SPAC3TRUK/Air-Link-Esp8266-/Progettazione_e_Documentazione/1.png

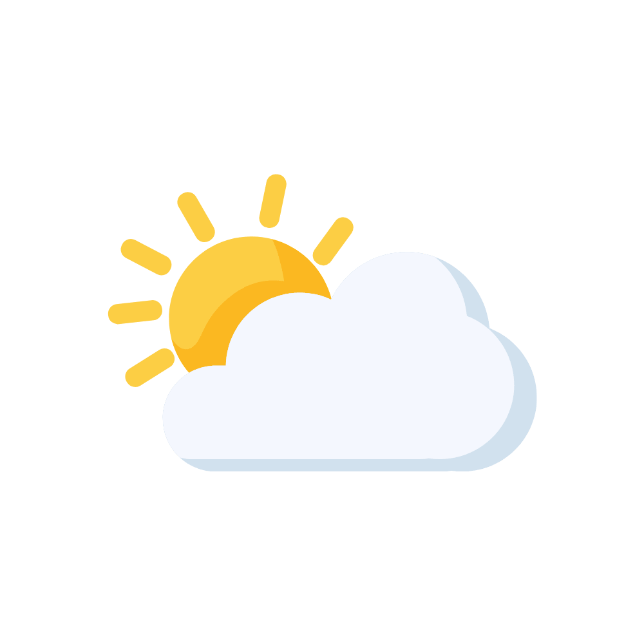
Progettazione_e_Documentazione/1.png
