SPAC3TRUK/Air-Link-Esp8266-/src/Air-Link/1.png.h

#include <pgmspace.h>


const unsigned char __1_png[] PROGMEM = {
  0x89, 0x50, 0x4e, 0x47, 0x0d, 0x0a, 0x1a, 0x0a, 0x00, 0x00, 0x00, 0x0d,
  0x49, 0x48, 0x44, 0x52, 0x00, 0x00, 0x03, 0xe8, 0x00, 0x00, 0x03, 0xe8,
  0x08, 0x03, 0x00, 0x00, 0x00, 0x7a, 0x7d, 0x24, 0xd6, 0x00, 0x00, 0x00,
  0x60, 0x50, 0x4c, 0x54, 0x45, 0x00, 0x00, 0x00, 0xfc, 0xd6, 0x60, 0xec,
  0xf2, 0xf9, 0xfc, 0xc3, 0x35, 0xfc, 0xcc, 0x41, 0xfd, 0xce, 0x41, 0xfd,
  0xcd, 0x42, 0xff, 0xcf, 0x41, 0xfd, 0xcd, 0x41, 0xfc, 0xcd, 0x41, 0xfb,
  0xcc, 0x40, 0xfc, 0xcd, 0x41, 0xfc, 0xcd, 0x44, 0xe8, 0xef, 0xf6, 0xde,
  0xe9, 0xf4, 0xfc, 0xcd, 0x41, 0xdf, 0xea, 0xf5, 0xe7, 0xf1, 0xf9, 0xe3,
  0xed, 0xf7, 0xe2, 0xec, 0xf6, 0xe4, 0xee, 0xf8, 0xf6, 0xd2, 0x6c, 0xf4,
  0xf7, 0xfe, 0xfc, 0xce, 0x44, 0xd1, 0xe1, 0xee, 0xfb, 0xb8, 0x21, 0xdb,
  0xe8, 0xf3, 0xf2, 0xf6, 0xfe, 0xef, 0xf4, 0xfc, 0xed, 0xe6, 0xd3, 0xf1,
  0xd9, 0x9e, 0xf4, 0xcd, 0x70, 0x1a, 0xa4, 0xb3, 0x24, 0x00, 0x00, 0x00,
  0x16, 0x74, 0x52, 0x4e, 0x53, 0x00, 0x13, 0xfe, 0xfe, 0xb9, 0x43, 0x76,
  0x29, 0x5e, 0xe3, 0xcf, 0xa1, 0xf3, 0xfa, 0xe5, 0x8b, 0xc7, 0x2c, 0x7c,
  0xa4, 0x52, 0xb4, 0x64, 0x0d, 0xfe, 0x50, 0x00, 0x00, 0x1b, 0xec, 0x49,
  0x44, 0x41, 0x54, 0x78, 0xda, 0xec, 0xc1, 0x81, 0x00, 0x00, 0x00, 0x00,
  0x80, 0xa0, 0xfd, 0xa9, 0x17, 0xa9, 0x02, 0x00, 0x00, 0x00, 0x00, 0x00,
  0x00, 0x00, 0x00, 0x00, 0x00, 0x00, 0x00, 0x00, 0x00, 0x00, 0x00, 0x00,
  0x00, 0x00, 0x00, 0x00, 0x00, 0x00, 0x00, 0x00, 0x00, 0x00, 0x00, 0x00,
  0x00, 0x00, 0x00, 0x00, 0x00, 0x00, 0x00, 0x00, 0x00, 0x00, 0x00, 0x00,
  0x00, 0x00, 0x00, 0x00, 0x00, 0x00, 0x00, 0x00, 0x00, 0x00, 0x00, 0x00,
  0x00, 0x00, 0x00, 0x00, 0x00, 0x60, 0xf6, 0xe0, 0x40, 0x00, 0x00, 0x00,
  0x00, 0x00, 0xc8, 0xff, 0xb5, 0x11, 0x54, 0x55, 0x55, 0x55, 0x55, 0x55,
  0x55, 0x55, 0x55, 0x55, 0x55, 0x55, 0x55, 0x55, 0x55, 0x55, 0x55, 0x55,
  0x55, 0x55, 0x55, 0x55, 0x55, 0x55, 0x55, 0x55, 0x55, 0x55, 0x55, 0x55,
  0x55, 0x55, 0x55, 0x55, 0x55, 0x55, 0x55, 0x55, 0x55, 0x55, 0x55, 0x55,
  0x55, 0x55, 0x55, 0x55, 0x55, 0x55, 0x55, 0x55, 0x55, 0x55, 0x55, 0x55,
  0x55, 0x55, 0x55, 0x55, 0x55, 0x85, 0x3d, 0x38, 0x10, 0x00, 0x00, 0x00,
  0x00, 0x00, 0xf2, 0x7f, 0x6d, 0x04, 0x55, 0x55, 0x55, 0x55, 0x55, 0x55,
  0x55, 0x55, 0x55, 0x55, 0x55, 0x55, 0x55, 0x55, 0x55, 0x55, 0x55, 0x55,
  0x55, 0x55, 0x55, 0x55, 0x55, 0x55, 0x55, 0x55, 0x55, 0x55, 0x55, 0x55,
  0x55, 0x55, 0x55, 0x55, 0x55, 0x55, 0x55, 0x55, 0x55, 0x55, 0x55, 0x55,
  0x55, 0x55, 0x55, 0x55, 0x55, 0x55, 0x55, 0x55, 0x55, 0x55, 0x55, 0x55,
  0x55, 0x55, 0x55, 0x55, 0x55, 0x61, 0x0f, 0x0e, 0x04, 0x00, 0x00, 0x00,
  0x00, 0x80, 0xfc, 0x5f, 0x1b, 0x41, 0x55, 0x55, 0x55, 0x55, 0x55, 0x55,
  0x55, 0x55, 0x55, 0x55, 0x55, 0x55, 0x55, 0x55, 0x55, 0x55, 0x55, 0x55,
  0x55, 0x55, 0x55, 0x55, 0x55, 0x55, 0x55, 0x55, 0x55, 0x55, 0x55, 0x55,
  0x55, 0x55, 0x55, 0x55, 0x55, 0x55, 0x55, 0x55, 0x55, 0x55, 0x55, 0x55,
  0x55, 0x55, 0x55, 0x55, 0x55, 0x55, 0x55, 0x55, 0x55, 0x55, 0x55, 0x55,
  0x55, 0x55, 0x55, 0x55, 0x55, 0xd8, 0xbb, 0xb7, 0xd4, 0xb8, 0x81, 0x20,
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
};
unsigned int __1_png_len = 7347;
